chris-pws/zero_cool/003.jpg

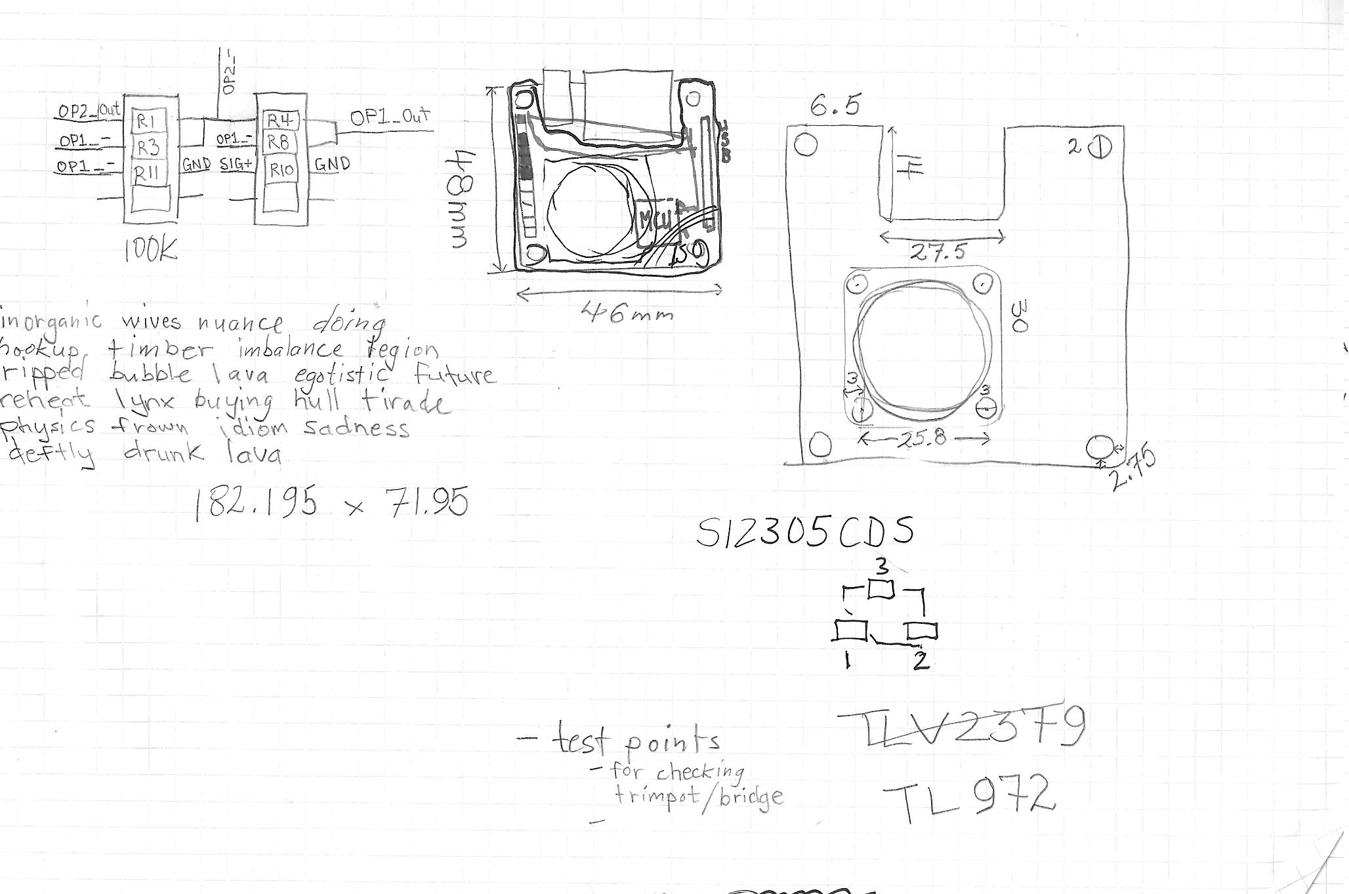
003.jpg
